todbot/QTPyNoisyBoi/firmware/arduino/QTPyNoisyBoi/seeed_pwm/wiring_pwm.cpp

/**
 * The MIT License (MIT)
 * 
 * Author: Hongtai Liu (lht856@foxmail.com)
 * 
 * Copyright (C) 2020  Seeed Technology Co.,Ltd. 
 * 
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
 * THE SOFTWARE IS PROVIDED "AS IS", WITHOUT WARRANTY OF ANY KIND, EXPRESS OR
 * IMPLIED, INCLUDING BUT NOT LIMITED TO THE WARRANTIES OF MERCHANTABILITY,
 * FITNESS FOR A PARTICULAR PURPOSE AND NONINFRINGEMENT. IN NO EVENT SHALL THE
 * AUTHORS OR COPYRIGHT HOLDERS BE LIABLE FOR ANY CLAIM, DAMAGES OR OTHER
 * LIABILITY, WHETHER IN AN ACTION OF CONTRACT, TORT OR OTHERWISE, ARISING FROM,
 * OUT OF OR IN CONNECTION WITH THE SOFTWARE OR THE USE OR OTHER DEALINGS IN
 * THE SOFTWARE.
 */

#include "wiring_pwm.h"
#include "wiring_private.h"

#if !defined(__SAMD51__)
// Wait for synchronization of registers between the clock domains
static __inline__ void syncTC_16(Tc* TCx) __attribute__((always_inline, unused));
static void syncTC_16(Tc* TCx) {
  while (TCx->COUNT16.STATUS.bit.SYNCBUSY);
}

// Wait for synchronization of registers between the clock domains
static __inline__ void syncTCC(Tcc* TCCx) __attribute__((always_inline, unused));
static void syncTCC(Tcc* TCCx) {
  while (TCCx->SYNCBUSY.reg & TCC_SYNCBUSY_MASK);
}
#endif

#if defined(__SAMD51__)
#define MAX_PERIOD 0xFF
#else
#define MAX_PERIOD 0xFFFF
#endif

// API uses 10 bit resolution
#define PWM_API_RESOLUTION 10

static inline unsigned long calcPrescaler(uint32_t frequency, uint32_t &period)
{
  //if it's a rest, set to 1Hz (below audio range)
  frequency = (frequency > 0 ? frequency : 1);
  //
  // Calculate best prescaler divider and comparator value for a 16 bit TC peripheral
  unsigned long prescalerConfigVal;

  period = F_CPU / frequency - 1;
  prescalerConfigVal = TC_CTRLA_PRESCALER_DIV1_Val;

  uint8_t i = 0;

  while (period > MAX_PERIOD)
  {
    if (i == 4 || i == 6 || i == 8) //DIV32 DIV128 and DIV512 are not available
      i++;
    period = F_CPU / frequency / (2 << i) - 1;
    i++;
  }

  #if defined(__SAMD51__)
  period = MAX_PERIOD;
  #else
  // Ensure that our period does not erode the API resolution
  if(period < (1<<PWM_API_RESOLUTION))
    period = (1<<PWM_API_RESOLUTION) - 1;
  #endif

  switch (i - 1)
  {
  case 0:
    prescalerConfigVal = TC_CTRLA_PRESCALER_DIV2_Val;
    break;

  case 1:
    prescalerConfigVal = TC_CTRLA_PRESCALER_DIV4_Val;
    break;

  case 2:
    prescalerConfigVal = TC_CTRLA_PRESCALER_DIV8_Val;
    break;

  case 3:
    prescalerConfigVal = TC_CTRLA_PRESCALER_DIV16_Val;
    break;

  case 5:
    prescalerConfigVal = TC_CTRLA_PRESCALER_DIV64_Val;
    break;

  case 7:
    prescalerConfigVal = TC_CTRLA_PRESCALER_DIV256_Val;
    break;

  case 9:
    prescalerConfigVal = TC_CTRLA_PRESCALER_DIV1024_Val;
    break;

  default:
    break;
  }

  return prescalerConfigVal;
}

void pwm(uint32_t outputPin, uint32_t frequency, uint32_t duty)
{
  PinDescription pinDesc = g_APinDescription[outputPin];
  uint32_t attr = pinDesc.ulPinAttribute;

#if defined(__SAMD51__)
  if (attr & (PIN_ATTR_PWM_E | PIN_ATTR_PWM_F | PIN_ATTR_PWM_G))
  {
    unsigned long prescalerConfigVal;
    uint32_t period;

    prescalerConfigVal = calcPrescaler(frequency, period);
    duty = map(duty, 0, (1<<PWM_API_RESOLUTION), 0, period);

    uint32_t tcNum = GetTCNumber(pinDesc.ulPWMChannel);
    uint8_t tcChannel = GetTCChannelNumber(pinDesc.ulPWMChannel);

    if (attr & PIN_ATTR_PWM_E)
      pinPeripheral(outputPin, PIO_TIMER);
    else if (attr & PIN_ATTR_PWM_F)
      pinPeripheral(outputPin, PIO_TIMER_ALT);
    else if (attr & PIN_ATTR_PWM_G)
      pinPeripheral(outputPin, PIO_TCC_PDEC);

    GCLK->PCHCTRL[GCLK_CLKCTRL_IDs[tcNum]].reg = GCLK_PCHCTRL_GEN_GCLK0_Val | (1 << GCLK_PCHCTRL_CHEN_Pos); //use clock generator 0

    // Set PORT
    if (tcNum >= TCC_INST_NUM)
    {
      // -- Configure TC
      Tc *TCx = (Tc *)GetTC(pinDesc.ulPWMChannel);

      //reset
      TCx->COUNT8.CTRLA.bit.SWRST = 1;
      while (TCx->COUNT8.SYNCBUSY.bit.SWRST)
        ;

      // Disable TCx
      TCx->COUNT8.CTRLA.bit.ENABLE = 0;
      while (TCx->COUNT8.SYNCBUSY.bit.ENABLE)
        ;
      // Set Timer counter Mode to 8 bits, normal PWM,
      TCx->COUNT8.CTRLA.reg = TC_CTRLA_MODE_COUNT8 | TC_CTRLA_PRESCALER(prescalerConfigVal);
      TCx->COUNT8.WAVE.reg = TC_WAVE_WAVEGEN_NPWM;

      while (TCx->COUNT8.SYNCBUSY.bit.CC0)
        ;
      // Set the initial value
      TCx->COUNT8.CC[tcChannel].reg = (uint8_t)duty;
      while (TCx->COUNT8.SYNCBUSY.bit.CC0)
        ;
      // Set PER to calculated period
      TCx->COUNT8.PER.reg = period;
      while (TCx->COUNT8.SYNCBUSY.bit.PER)
        ;
      // Enable TCx
      TCx->COUNT8.CTRLA.bit.ENABLE = 1;
      while (TCx->COUNT8.SYNCBUSY.bit.ENABLE)
        ;
    }
    else
    {
      // -- Configure TCC
      Tcc *TCCx = (Tcc *)GetTC(pinDesc.ulPWMChannel);

      TCCx->CTRLA.bit.SWRST = 1;
      while (TCCx->SYNCBUSY.bit.SWRST)
        ;

      // Disable TCCx
      TCCx->CTRLA.bit.ENABLE = 0;
      while (TCCx->SYNCBUSY.bit.ENABLE)
        ;
      // Set prescaler
      TCCx->CTRLA.reg = TC_CTRLA_PRESCALER(prescalerConfigVal) | TCC_CTRLA_PRESCSYNC_GCLK;

      // Set TCx as normal PWM
      TCCx->WAVE.reg = TCC_WAVE_WAVEGEN_NPWM;
      while (TCCx->SYNCBUSY.bit.WAVE)
        ;

      while (TCCx->SYNCBUSY.bit.CC0 || TCCx->SYNCBUSY.bit.CC1)
        ;
      // Set the initial value
      TCCx->CC[tcChannel].reg = (uint32_t)duty;
      while (TCCx->SYNCBUSY.bit.CC0 || TCCx->SYNCBUSY.bit.CC1)
        ;
      // Set PER to calculated period
      TCCx->PER.reg = period;
      while (TCCx->SYNCBUSY.bit.PER)
        ;
      // Enable TCCx
      TCCx->CTRLA.bit.ENABLE = 1;
      while (TCCx->SYNCBUSY.bit.ENABLE)
        ;
    }
    return;
  }

#else

  if ((attr & PIN_ATTR_PWM) == PIN_ATTR_PWM)
  {
    uint32_t prescalerConfigVal;
    uint32_t period;

    prescalerConfigVal = calcPrescaler(frequency, period);

    uint32_t tcNum = GetTCNumber(pinDesc.ulPWMChannel);
    uint8_t tcChannel = GetTCChannelNumber(pinDesc.ulPWMChannel);

    if (attr & PIN_ATTR_TIMER)
    {
#if !(ARDUINO_SAMD_VARIANT_COMPLIANCE >= 10603)
      // Compatibility for cores based on SAMD core <=1.6.2
      if (pinDesc.ulPinType == PIO_TIMER_ALT)
      {
        pinPeripheral(outputPin, PIO_TIMER_ALT);
      }
      else
#endif
      {
        pinPeripheral(outputPin, PIO_TIMER);
      }
    }
    else if ((attr & PIN_ATTR_TIMER_ALT) == PIN_ATTR_TIMER_ALT)
    {
      //this is on an alt timer
      pinPeripheral(outputPin, PIO_TIMER_ALT);
    }
    else
    {
      return;
    }

    uint16_t GCLK_CLKCTRL_IDs[] = {
        GCLK_CLKCTRL_ID(GCM_TCC0_TCC1), // TCC0
        GCLK_CLKCTRL_ID(GCM_TCC0_TCC1), // TCC1
        GCLK_CLKCTRL_ID(GCM_TCC2_TC3),  // TCC2
        GCLK_CLKCTRL_ID(GCM_TCC2_TC3),  // TC3
        GCLK_CLKCTRL_ID(GCM_TC4_TC5),   // TC4
        GCLK_CLKCTRL_ID(GCM_TC4_TC5),   // TC5
        GCLK_CLKCTRL_ID(GCM_TC6_TC7),   // TC6
        GCLK_CLKCTRL_ID(GCM_TC6_TC7),   // TC7
    };
    GCLK->CLKCTRL.reg = (uint16_t)(GCLK_CLKCTRL_CLKEN | GCLK_CLKCTRL_GEN_GCLK0 | GCLK_CLKCTRL_IDs[tcNum]);
    while (GCLK->STATUS.bit.SYNCBUSY == 1)
      ;

    // Set PORT
    if (tcNum >= TCC_INST_NUM)
    {
      duty = mapResolution(duty, 10, 16);
      // -- Configure TC
      Tc *TCx = (Tc *)GetTC(pinDesc.ulPWMChannel);
      // Disable TCx
      TCx->COUNT16.CTRLA.bit.ENABLE = 0;
      syncTC_16(TCx);
      // Set Timer counter Mode to 16 bits, normal PWM
      TCx->COUNT16.CTRLA.reg |= TC_CTRLA_MODE_COUNT16 | TC_CTRLA_WAVEGEN_NPWM | TC_CTRLA_PRESCALER(prescalerConfigVal);
      syncTC_16(TCx);
      // Set the initial value
      TCx->COUNT16.CC[tcChannel].reg = (uint32_t)duty;
      syncTC_16(TCx);
      // Enable TCx
      TCx->COUNT16.CTRLA.bit.ENABLE = 1;
      syncTC_16(TCx);
    }
    else
    {
      duty = map(duty, 0, (1<<PWM_API_RESOLUTION), 0, period);
      // -- Configure TCC
      Tcc *TCCx = (Tcc *)GetTC(pinDesc.ulPWMChannel);
      // Disable TCCx
      TCCx->CTRLA.bit.ENABLE = 0;
      syncTCC(TCCx);
      // Set prescaler
      TCCx->CTRLA.bit.PRESCALER = prescalerConfigVal;
      syncTCC(TCCx);
      // Set TCCx as normal PWM
      TCCx->WAVE.reg |= TCC_WAVE_WAVEGEN_NPWM;
      syncTCC(TCCx);
      // Set the initial value
      TCCx->CC[tcChannel].reg = (uint32_t)duty;
      syncTCC(TCCx);
      // Set PER to calculated period
      TCCx->PER.reg = period;
      syncTCC(TCCx);
      // Enable TCCx
      TCCx->CTRLA.bit.ENABLE = 1;
      syncTCC(TCCx);
    }
    return;
  }
#endif
}

void noPwm(uint32_t outputPin)
{
  PinDescription pinDesc = g_APinDescription[outputPin];
  uint32_t attr = pinDesc.ulPinAttribute;

#if defined(__SAMD51__)
  if (attr & (PIN_ATTR_PWM_E | PIN_ATTR_PWM_F | PIN_ATTR_PWM_G))
  {

    uint32_t tcNum = GetTCNumber(pinDesc.ulPWMChannel);

    if (attr & PIN_ATTR_PWM_E)
      pinPeripheral(outputPin, PIO_TIMER);
    else if (attr & PIN_ATTR_PWM_F)
      pinPeripheral(outputPin, PIO_TIMER_ALT);
    else if (attr & PIN_ATTR_PWM_G)
      pinPeripheral(outputPin, PIO_TCC_PDEC);

    GCLK->PCHCTRL[GCLK_CLKCTRL_IDs[tcNum]].reg = GCLK_PCHCTRL_GEN_GCLK0_Val | (1 << GCLK_PCHCTRL_CHEN_Pos); //use clock generator 0

    // Set PORT
    if (tcNum >= TCC_INST_NUM)
    {
      // -- Configure TC
      Tc *TCx = (Tc *)GetTC(pinDesc.ulPWMChannel);

      //reset
      TCx->COUNT8.CTRLA.bit.SWRST = 1;
      while (TCx->COUNT8.SYNCBUSY.bit.SWRST)
        ;

      // Disable TCx
      TCx->COUNT8.CTRLA.bit.ENABLE = 0;
      while (TCx->COUNT8.SYNCBUSY.bit.ENABLE)
        ;
    }
    else
    {
      // -- Configure TCC
      Tcc *TCCx = (Tcc *)GetTC(pinDesc.ulPWMChannel);

      TCCx->CTRLA.bit.SWRST = 1;
      while (TCCx->SYNCBUSY.bit.SWRST)
        ;

      // Disable TCCx
      TCCx->CTRLA.bit.ENABLE = 0;
      while (TCCx->SYNCBUSY.bit.ENABLE)
        ;
    }
    return;
  }

#else
  if ((attr & PIN_ATTR_PWM) == PIN_ATTR_PWM)
  {

    uint32_t tcNum = GetTCNumber(pinDesc.ulPWMChannel);
    uint8_t tcChannel = GetTCChannelNumber(pinDesc.ulPWMChannel);

    if (attr & PIN_ATTR_TIMER)
    {
#if !(ARDUINO_SAMD_VARIANT_COMPLIANCE >= 10603)
      // Compatibility for cores based on SAMD core <=1.6.2
      if (pinDesc.ulPinType == PIO_TIMER_ALT)
      {
        pinPeripheral(outputPin, PIO_TIMER_ALT);
      }
      else
#endif
      {
        pinPeripheral(outputPin, PIO_TIMER);
      }
    }
    else if ((attr & PIN_ATTR_TIMER_ALT) == PIN_ATTR_TIMER_ALT)
    {
      //this is on an alt timer
      pinPeripheral(outputPin, PIO_TIMER_ALT);
    }
    else
    {
      return;
    }

    uint16_t GCLK_CLKCTRL_IDs[] = {
        GCLK_CLKCTRL_ID(GCM_TCC0_TCC1), // TCC0
        GCLK_CLKCTRL_ID(GCM_TCC0_TCC1), // TCC1
        GCLK_CLKCTRL_ID(GCM_TCC2_TC3),  // TCC2
        GCLK_CLKCTRL_ID(GCM_TCC2_TC3),  // TC3
        GCLK_CLKCTRL_ID(GCM_TC4_TC5),   // TC4
        GCLK_CLKCTRL_ID(GCM_TC4_TC5),   // TC5
        GCLK_CLKCTRL_ID(GCM_TC6_TC7),   // TC6
        GCLK_CLKCTRL_ID(GCM_TC6_TC7),   // TC7
    };
    GCLK->CLKCTRL.reg = (uint16_t)(GCLK_CLKCTRL_CLKEN | GCLK_CLKCTRL_GEN_GCLK0 | GCLK_CLKCTRL_IDs[tcNum]);
    while (GCLK->STATUS.bit.SYNCBUSY == 1)
      ;

    // Set PORT
    if (tcNum >= TCC_INST_NUM)
    {
      // -- Configure TC
      Tc *TCx = (Tc *)GetTC(pinDesc.ulPWMChannel);
      // Disable TCx
      TCx->COUNT16.CTRLA.bit.ENABLE = 0;
      syncTC_16(TCx);
    }
    else
    {
      // -- Configure TCC
      Tcc *TCCx = (Tcc *)GetTC(pinDesc.ulPWMChannel);
      // Disable TCCx
      TCCx->CTRLA.bit.ENABLE = 0;
      syncTCC(TCCx);
    }
    return;
  }
#endif
}
