todbot/QTPyNoisyBoi/firmware/arduino/QTPyNoisyBoi/calibration.h

//  experimentally-measured calibration values

voltage_calibration cals_a[] =
    {
     {-3.34, 65535},
     {0.0, 43675},
     {6.69, 0}
    };

voltage_calibration cals_b[] =
    {
     {-3.40, 65535},
     {0.0, 43535},
     {6.73, 0},
    };

voltage_calibration cals_c[] =
    {
     {-3.3, 65535}, // FIXME this just made up
     {6.7, 0}
    };
